LAxt03/Lumos-Link-IoT-2025/DIY - Bilder/Schritt 1 -- ESP32 einklinken.jpeg

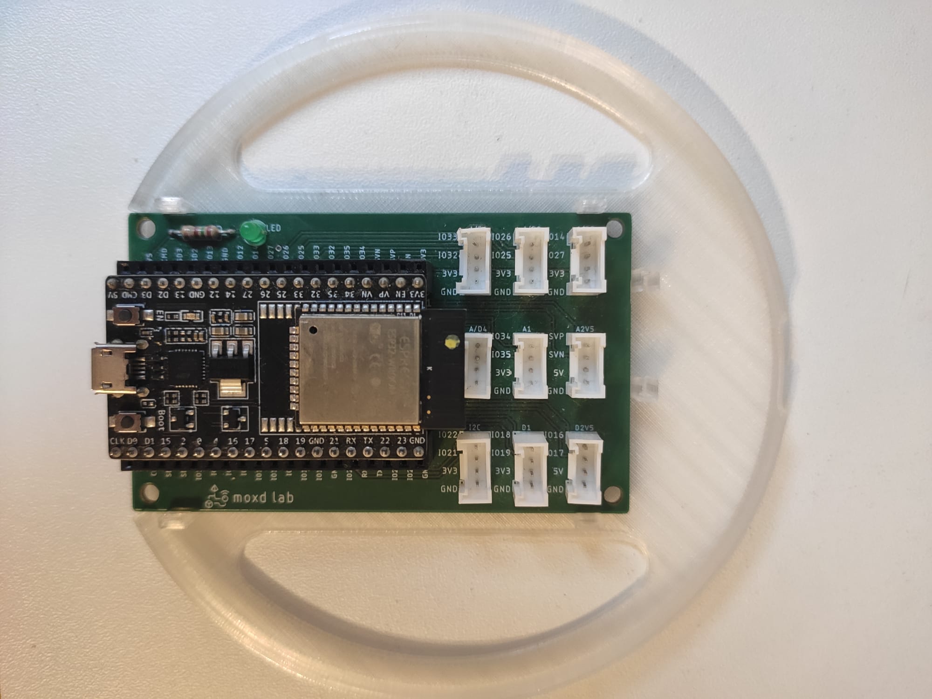
DIY - Bilder/Schritt 1 -- ESP32 einklinken.jpeg
