LAxt03/Lumos-Link-IoT-2025/DIY - Bilder/Schritt 2 -- Sound-Sensor einklinken.jpeg

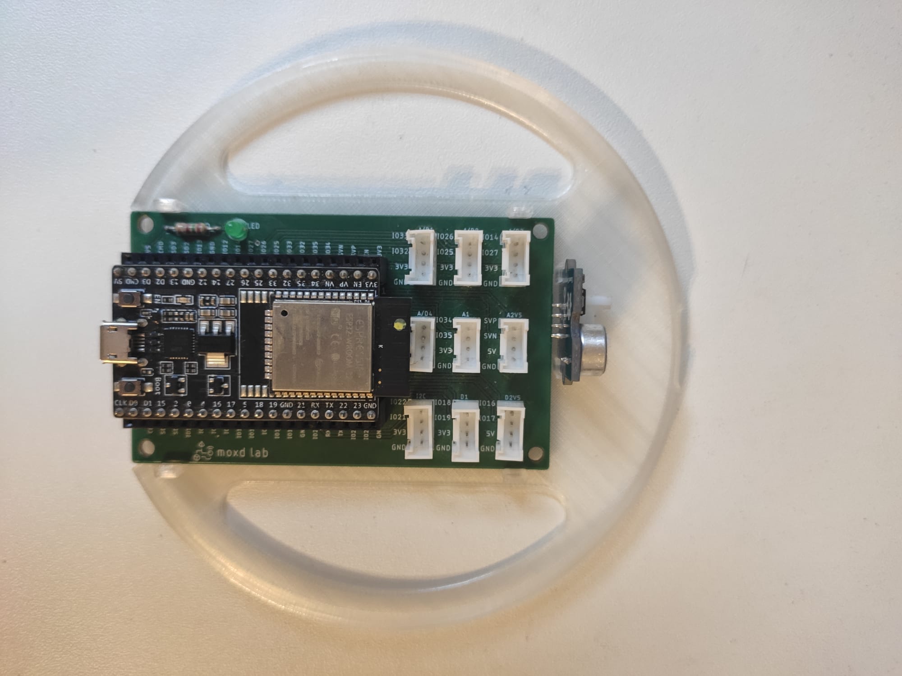
DIY - Bilder/Schritt 2 -- Sound-Sensor einklinken.jpeg
