LAxt03/Lumos-Link-IoT-2025/DIY - Bilder/Schritt 3 -- LED-Ring einsetzen.jpeg

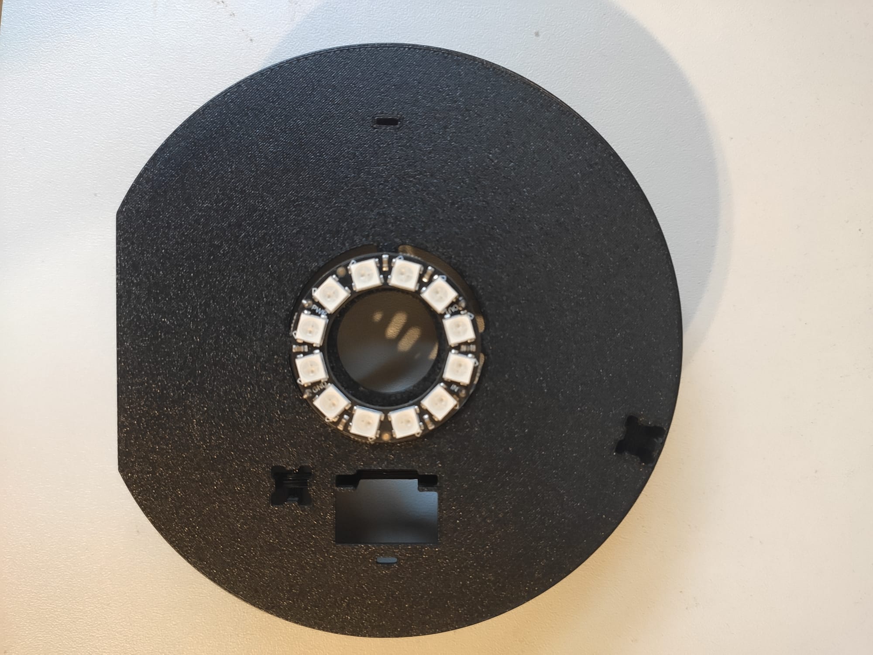
DIY - Bilder/Schritt 3 -- LED-Ring einsetzen.jpeg
