LAxt03/Lumos-Link-IoT-2025/DIY - Bilder/Schritt 4 -- LED-Ring-Kappe einklinken.jpeg

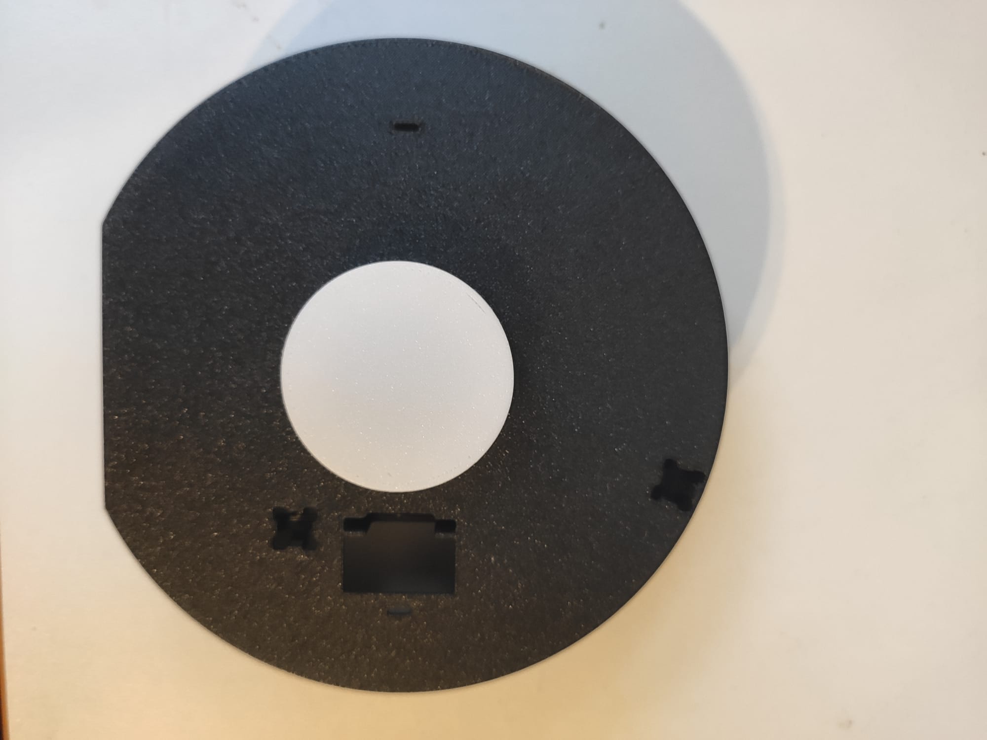
DIY - Bilder/Schritt 4 -- LED-Ring-Kappe einklinken.jpeg
