LAxt03/Lumos-Link-IoT-2025/DIY - Bilder/Schritt 5 -- Taster einsetzten.jpeg

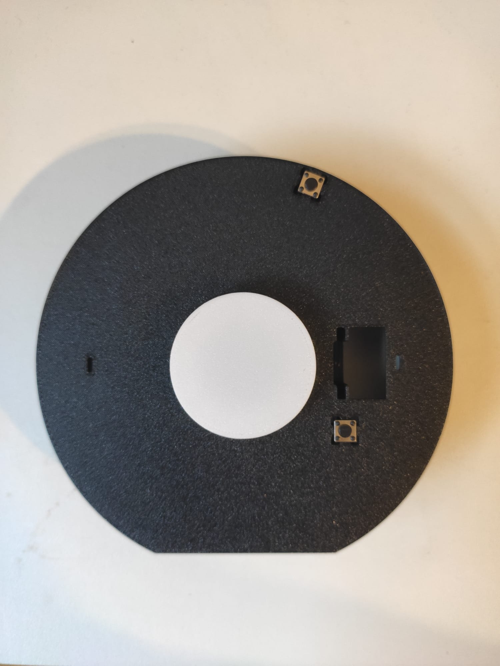
DIY - Bilder/Schritt 5 -- Taster einsetzten.jpeg
