LAxt03/Lumos-Link-IoT-2025/DIY - Bilder/Schritt 7 -- Jumperkabel am Lichtsensor anschließen.jpeg

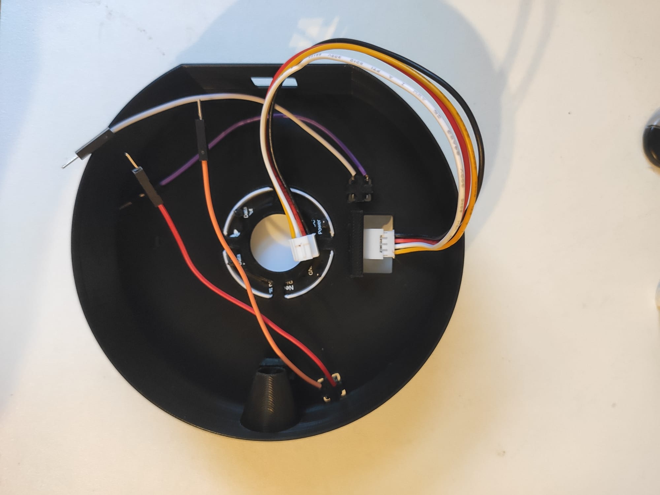
DIY - Bilder/Schritt 7 -- Jumperkabel am Lichtsensor anschließen.jpeg
