LAxt03/Lumos-Link-IoT-2025/DIY - Bilder/Schritt 8 -- Jumperkabel an Sound-Sensor anschließen.jpeg

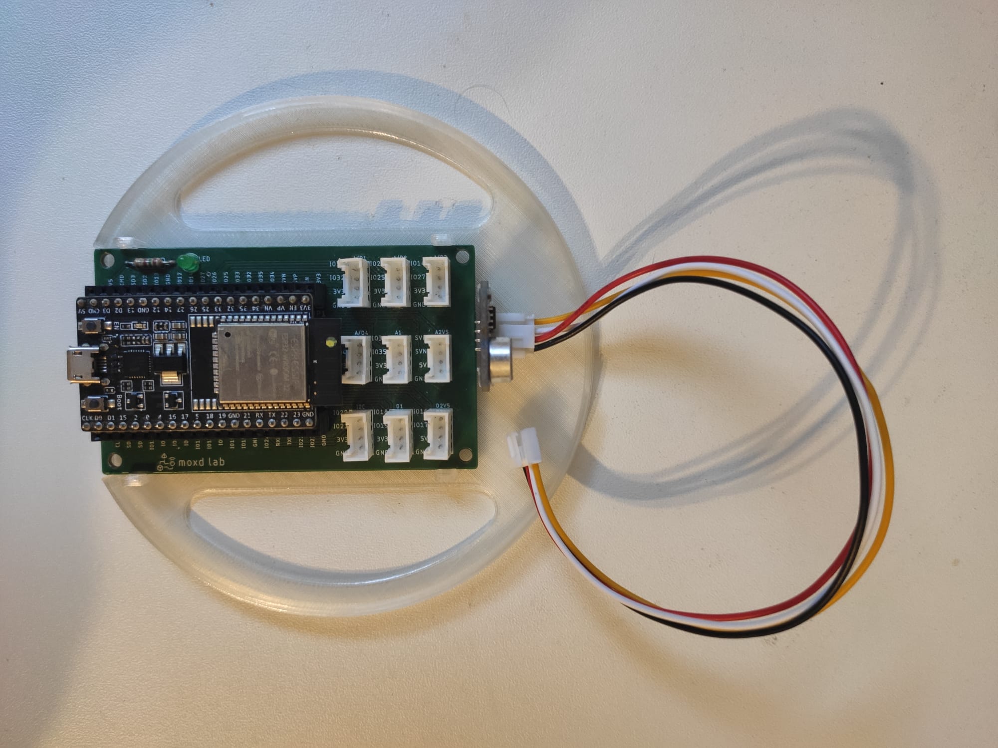
DIY - Bilder/Schritt 8 -- Jumperkabel an Sound-Sensor anschließen.jpeg
