LAxt03/Lumos-Link-IoT-2025/DIY - Bilder/Schritt 12 -- Innerer Taster an ESP32 anschließen.jpeg

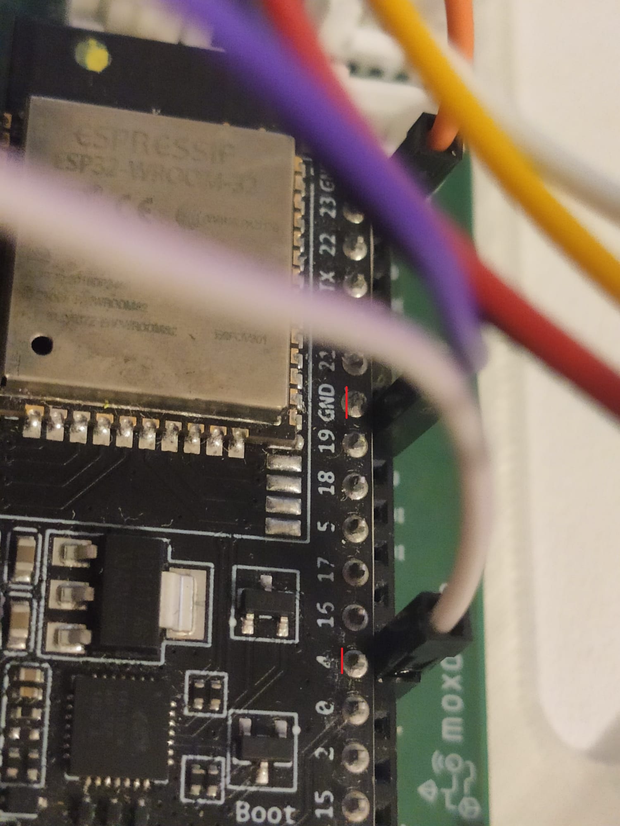
DIY - Bilder/Schritt 12 -- Innerer Taster an ESP32 anschließen.jpeg
