LAxt03/Lumos-Link-IoT-2025/DIY - Bilder/Schritt 14 -- Lichtsensor Jumperkabel an GPIO33 anschließen.jpeg

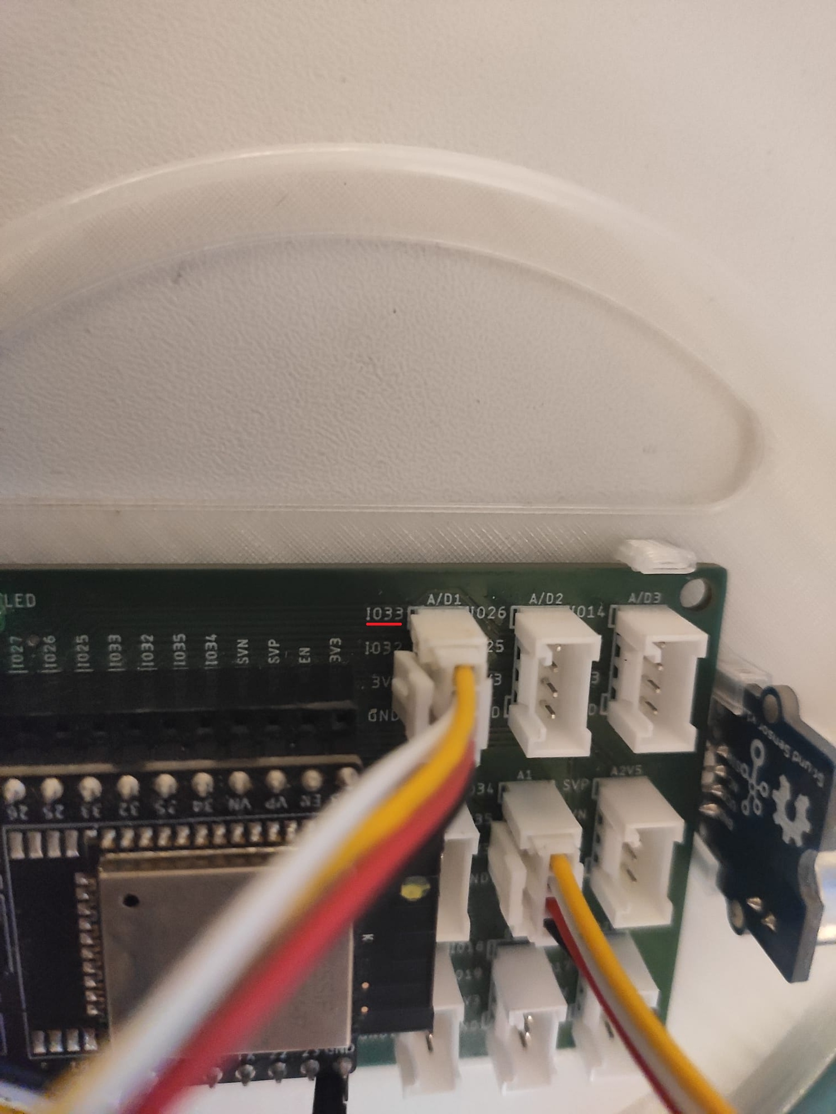
DIY - Bilder/Schritt 14 -- Lichtsensor Jumperkabel an GPIO33 anschließen.jpeg
