LAxt03/Lumos-Link-IoT-2025/DIY - Bilder/Schritt 15 -- Plastikkappe auf Plastikbase stecken.jpeg

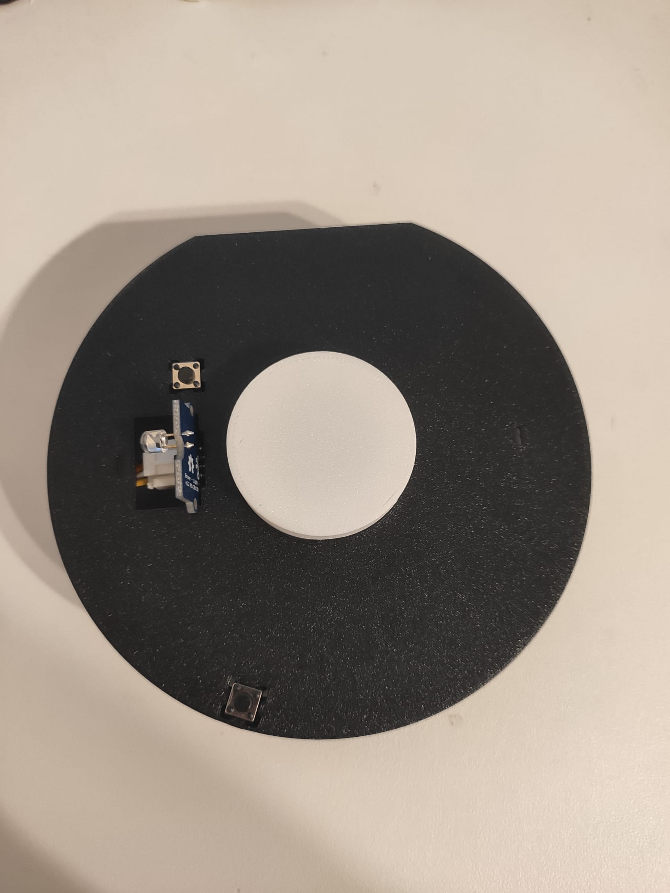
DIY - Bilder/Schritt 15 -- Plastikkappe auf Plastikbase stecken.jpeg
