LAxt03/Lumos-Link-IoT-2025/DIY - Bilder/Schritt 16 -- Stabilitätsring auf Plastikbase setzen.jpeg

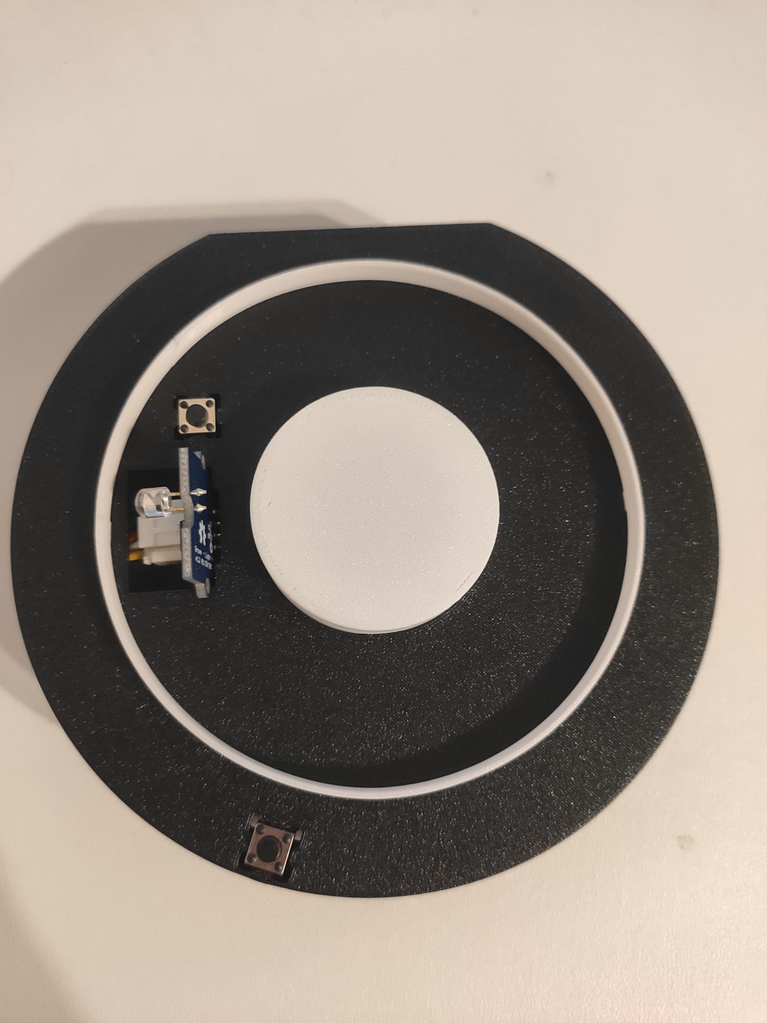
DIY - Bilder/Schritt 16 -- Stabilitätsring auf Plastikbase setzen.jpeg
